yoshiwars/Arduinoscope/3D Print Files/STL/Focus socket-Cut.stl

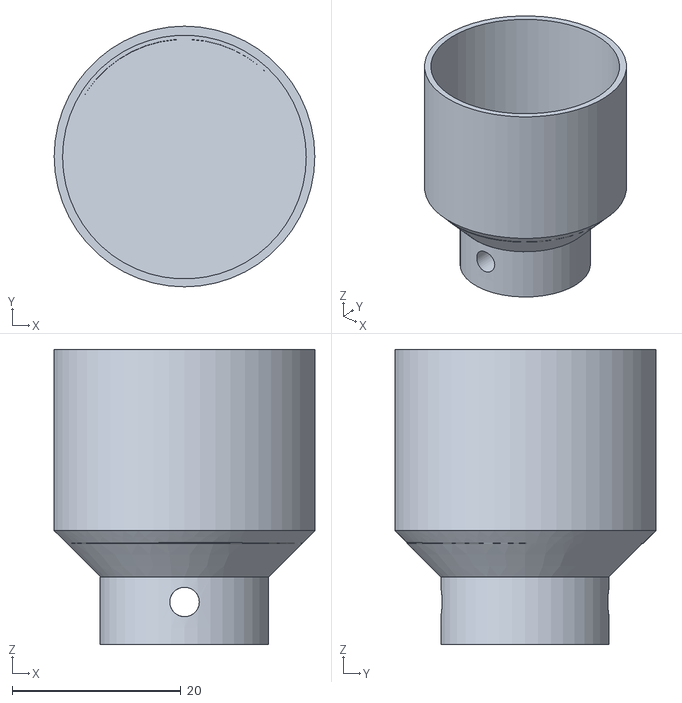
[picture p15: CAD file, 2023-07-31]
3D Print Files/STL/Focus socket-Cut.stl
30.9 x 30.9 x 35.0
