yoshiwars/Arduinoscope/3D Print Files/Binoculurs/Box.stl

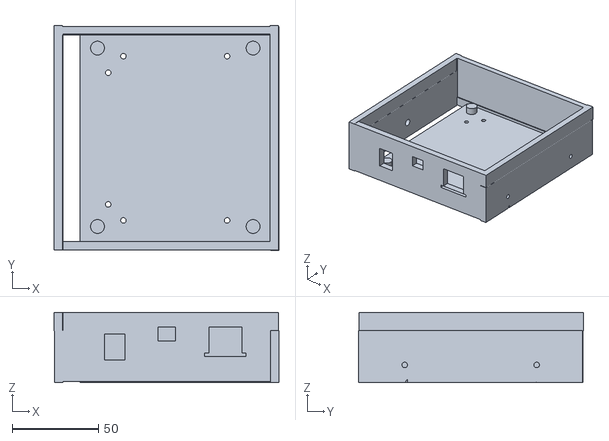
[picture p16: CAD file, 2023-07-31]
3D Print Files/Binoculurs/Box.stl
130.2 x 130.3 x 40.5
