yoshiwars/Arduinoscope/3D Print Files/Designs/BottomGear.FCStd

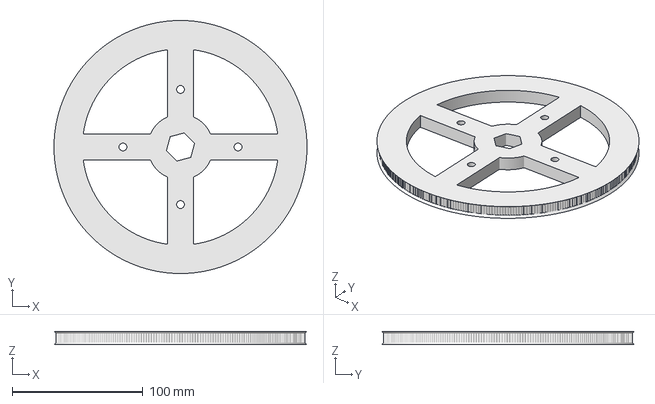
[picture p17: CAD file, 2023-02-02]
3D Print Files/Designs/BottomGear.FCStd
193.5 x 193.5 x 10.0 mm
