yoshiwars/Arduinoscope/3D Print Files/STL/MotorFocuser-Fusion.stl

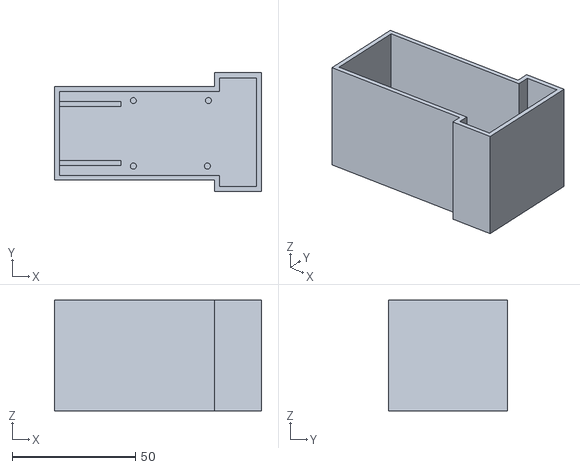
[picture p18: CAD file, 2023-03-01]
3D Print Files/STL/MotorFocuser-Fusion.stl
84.0 x 48.1 x 45.0
