yoshiwars/Arduinoscope/3D Print Files/Binoculurs/CameraMountSpacer.3mf

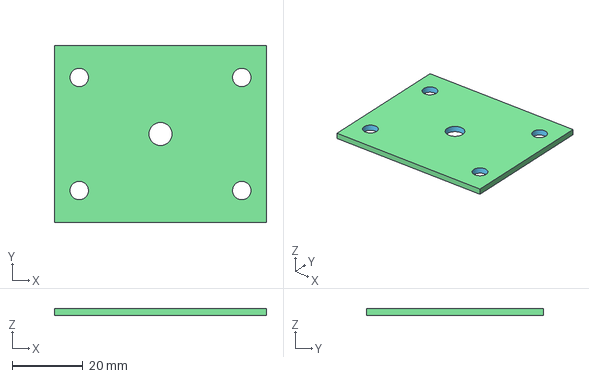
[picture p19: CAD file, 2023-07-31]
3D Print Files/Binoculurs/CameraMountSpacer.3mf
60.0 x 50.0 x 2.00 mm
