yoshiwars/Arduinoscope/3D Print Files/Designs/Telescope Holder.FCStd

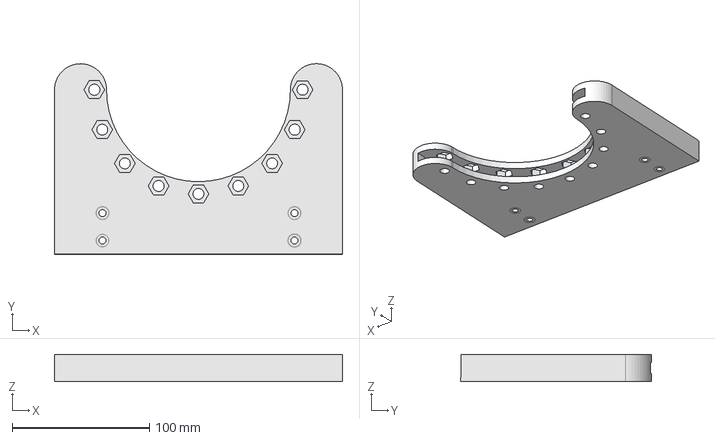
[picture p20: CAD file, 2023-02-02]
3D Print Files/Designs/Telescope Holder.FCStd
210.0 x 139.0 x 20.0 mm
