yoshiwars/Arduinoscope/3D Print Files/Binoculurs/AxisSpacerCut.stl

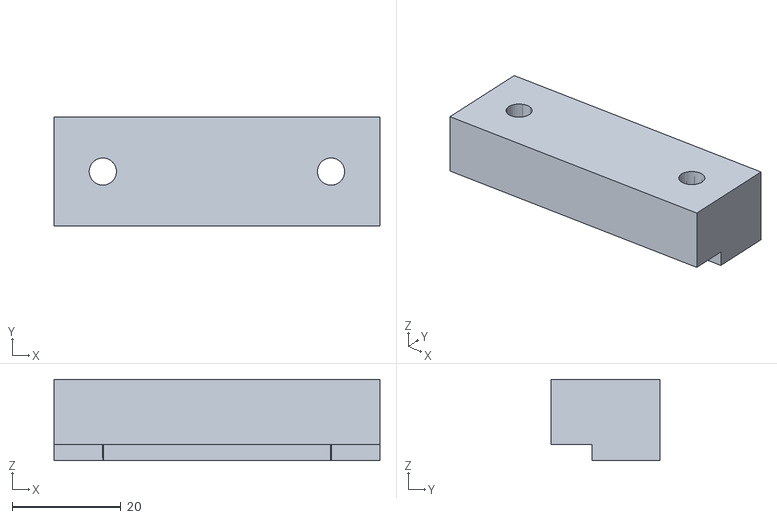
[picture p21: CAD file, 2023-07-31]
3D Print Files/Binoculurs/AxisSpacerCut.stl
60.0 x 20.0 x 15.0
