yoshiwars/Arduinoscope/3D Print Files/STL/Hand Control Top.stl

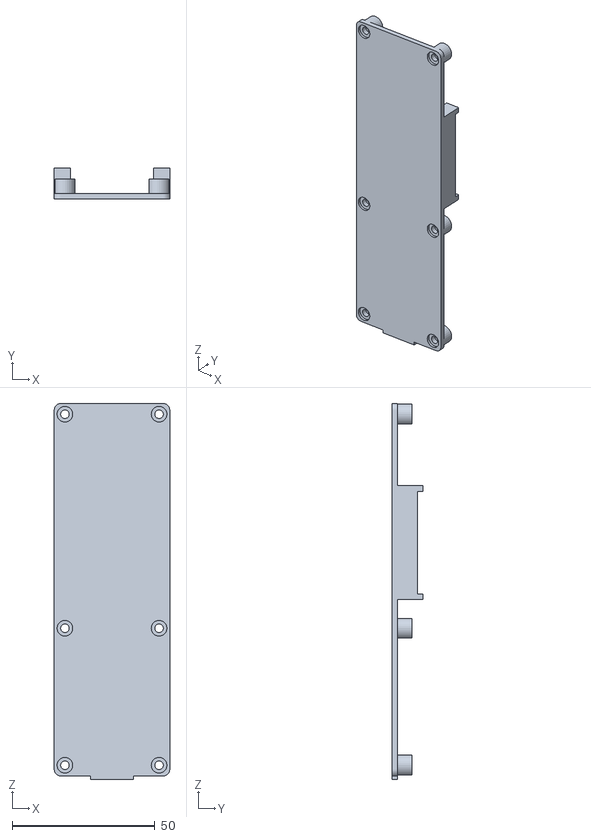
[picture p22: CAD file, 2023-02-02]
3D Print Files/STL/Hand Control Top.stl
40.5 x 11.0 x 131.8
