yoshiwars/Arduinoscope/3D Print Files/Binoculurs/Motor and Board Mount.3mf

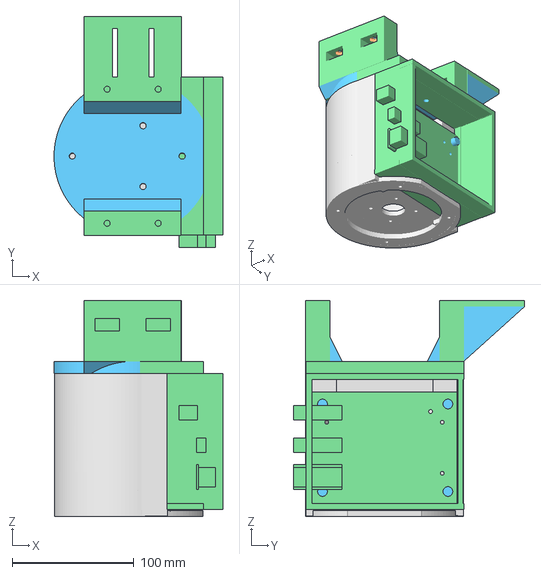
[picture p23: CAD file, 2023-07-31]
3D Print Files/Binoculurs/Motor and Board Mount.3mf
139.0 x 190.4 x 177.7 mm
