yoshiwars/Arduinoscope/3D Print Files/STL/Altitude Spacer v2.stl

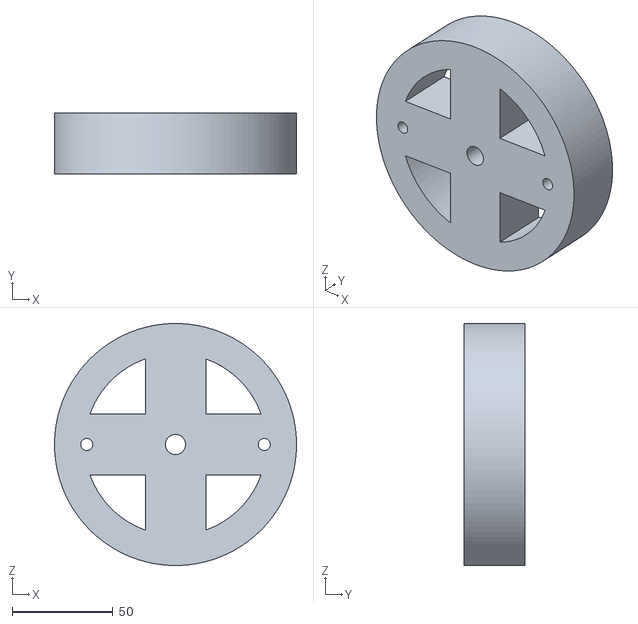
[picture p24: CAD file, 2023-02-02]
3D Print Files/STL/Altitude Spacer v2.stl
120.0 x 30.0 x 120.0
