yoshiwars/Arduinoscope/3D Print Files/Binoculurs/Top.3mf

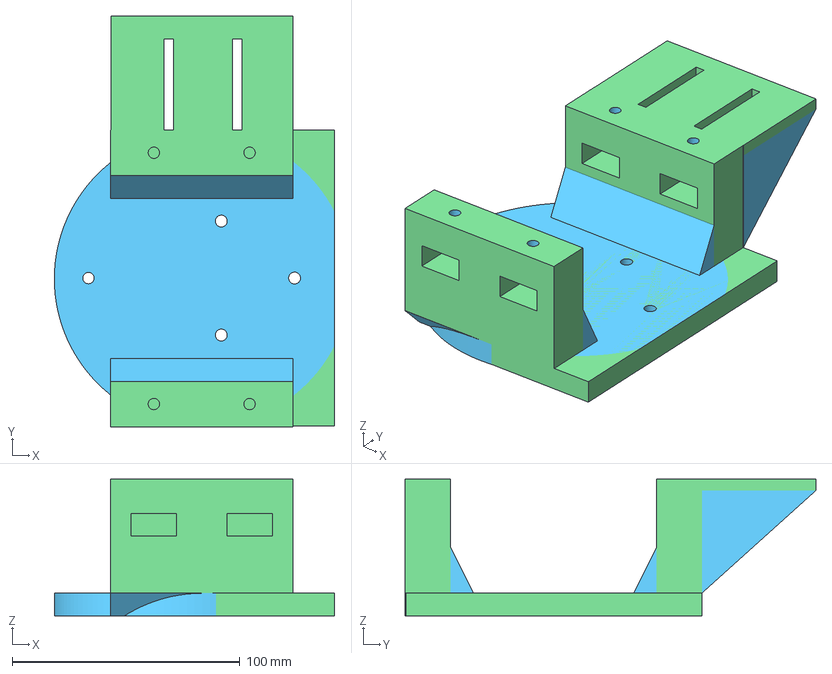
[picture p25: CAD file, 2023-07-31]
3D Print Files/Binoculurs/Top.3mf
123.0 x 180.4 x 60.0 mm
