yoshiwars/Arduinoscope/3D Print Files/STL/Hand Control Stand Holder.stl

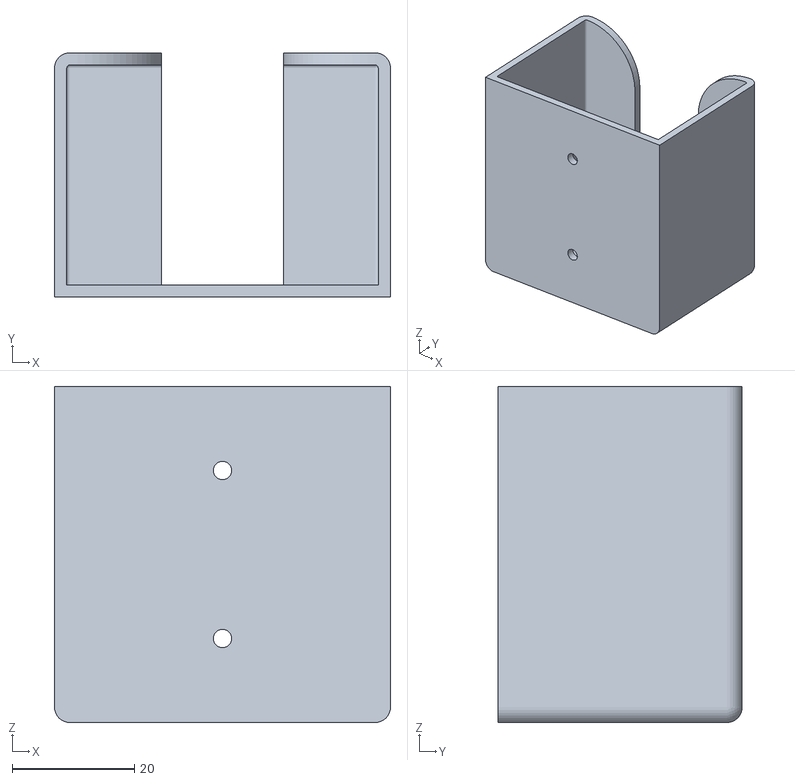
[picture p26: CAD file, 2023-02-02]
3D Print Files/STL/Hand Control Stand Holder.stl
55.0 x 40.0 x 55.0
