yoshiwars/Arduinoscope/3D Print Files/Binoculurs/StorageBox.3mf

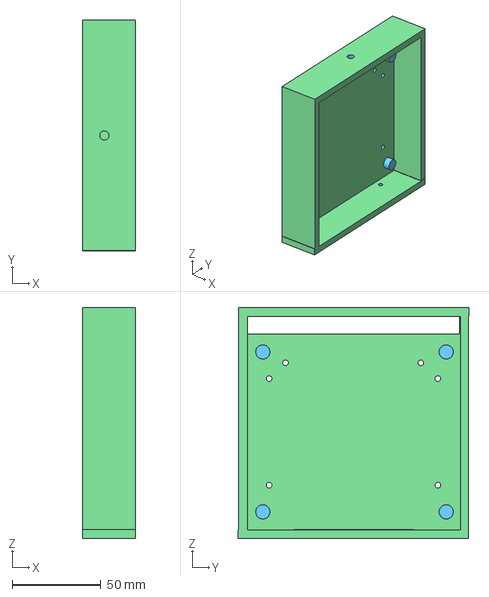
[picture p27: CAD file, 2023-07-31]
3D Print Files/Binoculurs/StorageBox.3mf
30.0 x 130.0 x 130.0 mm
