yoshiwars/Arduinoscope/3D Print Files/STL/1.25 Inch Lens Holder Top.stl

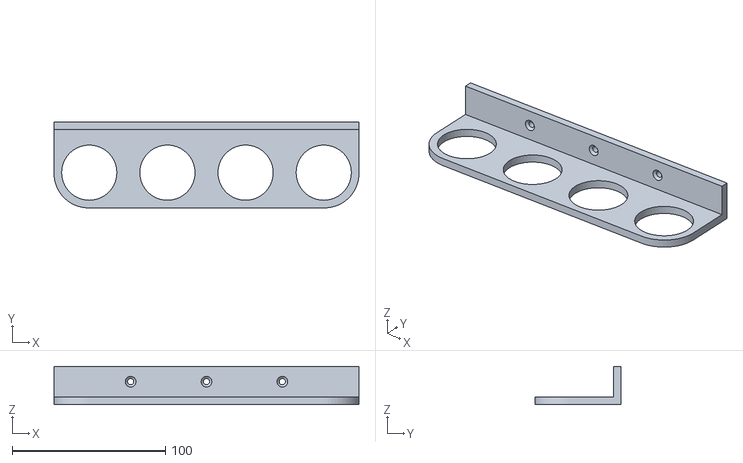
[picture p28: CAD file, 2023-02-02]
3D Print Files/STL/1.25 Inch Lens Holder Top.stl
199.0 x 56.0 x 25.0
