yoshiwars/Arduinoscope/3D Print Files/Binoculurs/ScreenHolder.stl

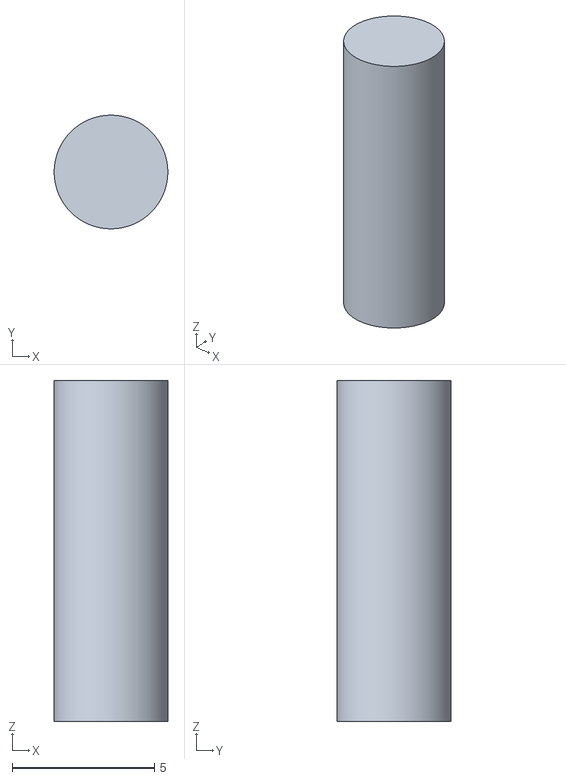
[picture p29: CAD file, 2023-07-31]
3D Print Files/Binoculurs/ScreenHolder.stl
4.00 x 4.00 x 12.0
