yoshiwars/Arduinoscope/3D Print Files/STL/2 inch Lens Holder Top.stl

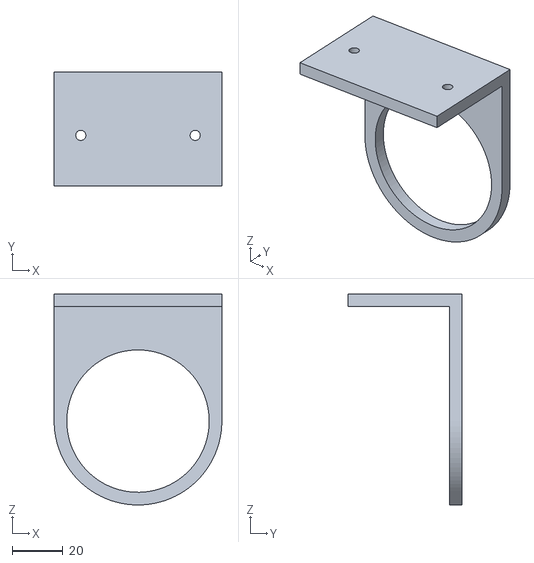
[picture p30: CAD file, 2023-02-02]
3D Print Files/STL/2 inch Lens Holder Top.stl
66.0 x 45.0 x 83.0
