yoshiwars/Arduinoscope/3D Print Files/Binoculurs/Handheld.3mf

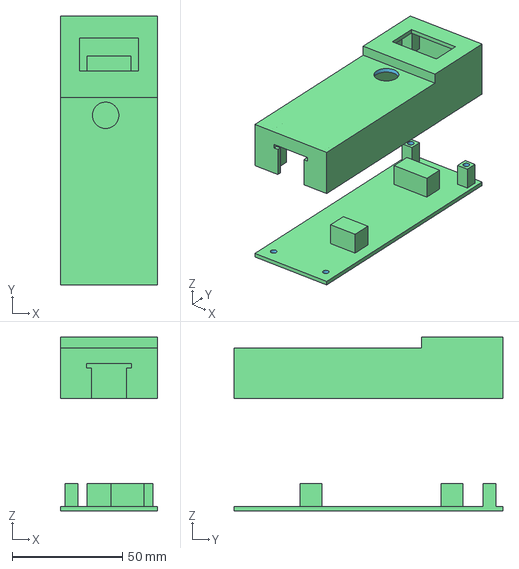
[picture p31: CAD file, 2023-07-31]
3D Print Files/Binoculurs/Handheld.3mf
44.0 x 122.0 x 79.0 mm
