yoshiwars/Arduinoscope/3D Print Files/STL/2 inch Lens Holder Bottom.stl

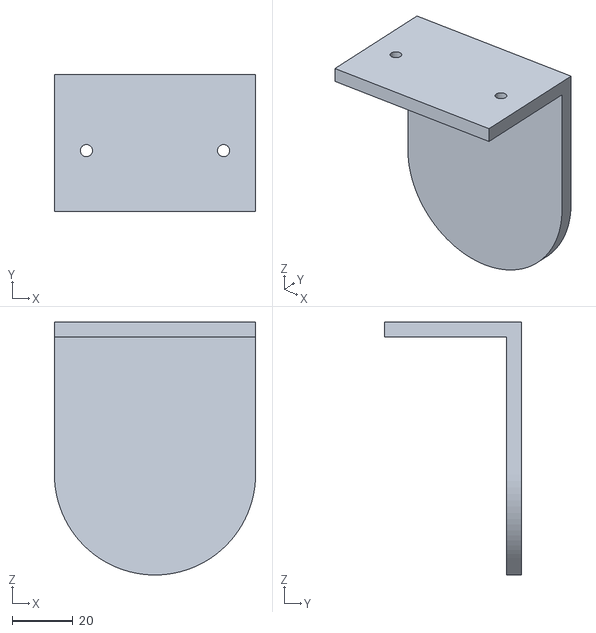
[picture p32: CAD file, 2023-02-02]
3D Print Files/STL/2 inch Lens Holder Bottom.stl
66.0 x 45.0 x 83.0
