yoshiwars/Arduinoscope/3D Print Files/STL/Hand Control Bottom.stl

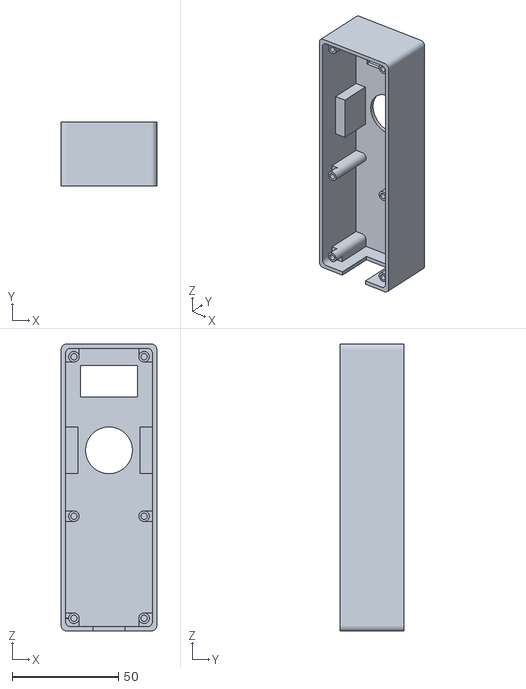
[picture p33: CAD file, 2023-02-02]
3D Print Files/STL/Hand Control Bottom.stl
45.0 x 30.0 x 135.0
