yoshiwars/Arduinoscope/3D Print Files/STL/Electronics Box.stl

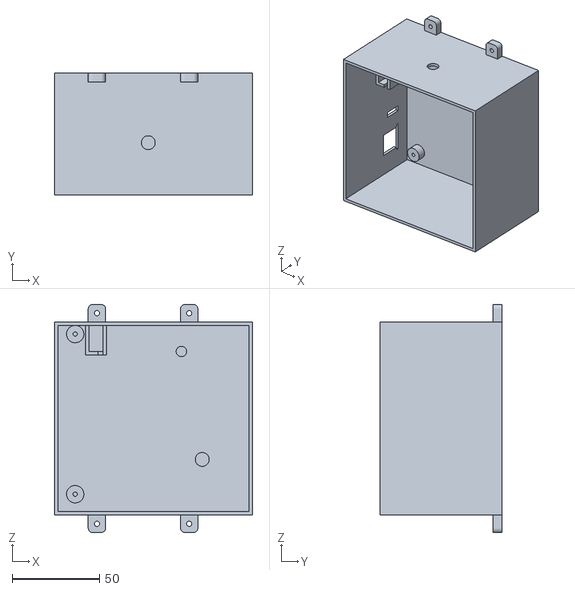
[picture p34: CAD file, 2023-02-02]
3D Print Files/STL/Electronics Box.stl
114.0 x 70.0 x 131.0
