yoshiwars/Arduinoscope/3D Print Files/STL/1.25 Inch Lens Holder Bottom.stl

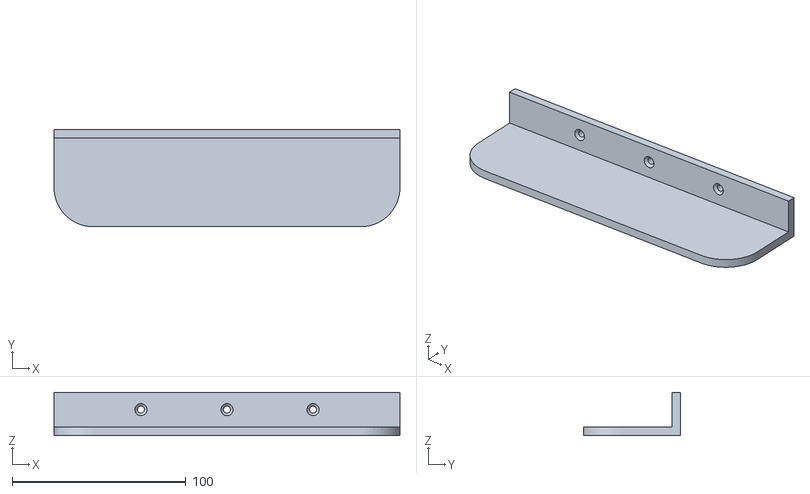
[picture p35: CAD file, 2023-02-02]
3D Print Files/STL/1.25 Inch Lens Holder Bottom.stl
199.0 x 56.0 x 25.0
